4pplet/cyber60/readme-images/cyber60-ALPS_Rev_D1_Tray.png

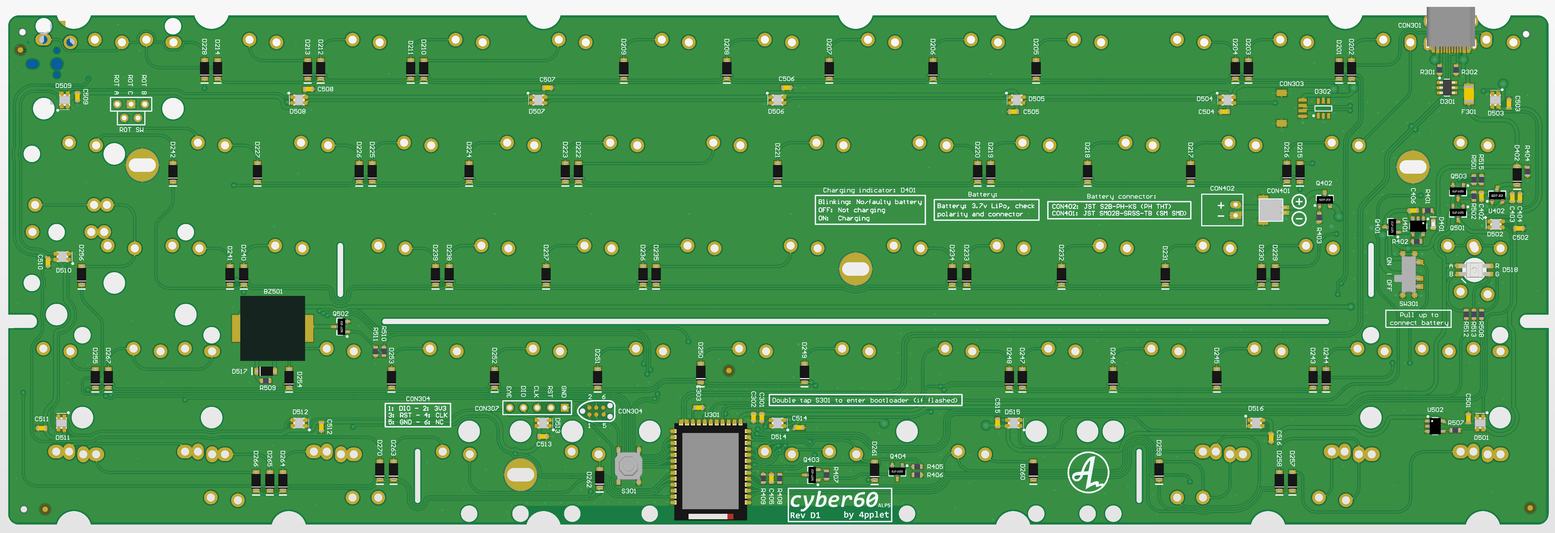
readme-images/cyber60-ALPS_Rev_D1_Tray.png
