4pplet/cyber60/readme-images/layout_support_cyber60_Rev_C.jpg

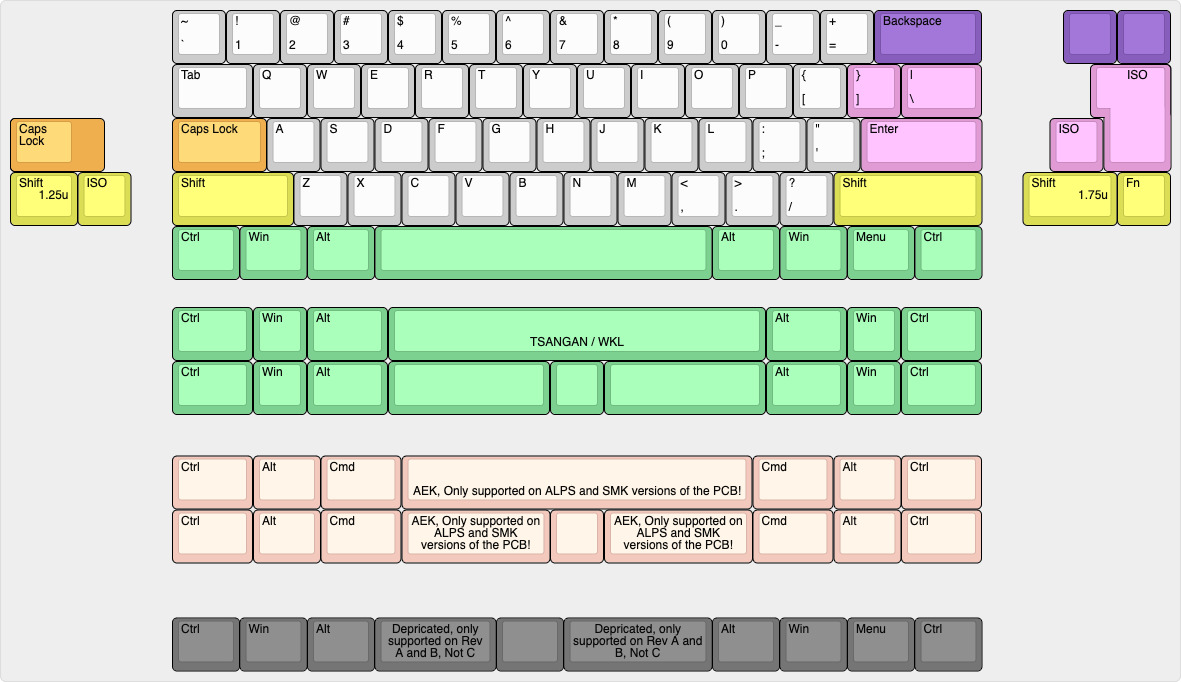
readme-images/layout_support_cyber60_Rev_C.jpg
